wlowi/PPMInspect/PPMInspect/ScopeScreen.cpp

/*
  PPMInspect. A PPM signal analysis tool.

  MIT License

  Copyright (c) 2023 wlowi

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
  THE SOFTWARE IS PROVIDED "AS IS", WITHOUT WARRANTY OF ANY KIND, EXPRESS OR
  IMPLIED, INCLUDING BUT NOT LIMITED TO THE WARRANTIES OF MERCHANTABILITY,
  FITNESS FOR A PARTICULAR PURPOSE AND NONINFRINGEMENT. IN NO EVENT SHALL THE
  AUTHORS OR COPYRIGHT HOLDERS BE LIABLE FOR ANY CLAIM, DAMAGES OR OTHER
  LIABILITY, WHETHER IN AN ACTION OF CONTRACT, TORT OR OTHERWISE, ARISING FROM,
  OUT OF OR IN CONNECTION WITH THE SOFTWARE OR THE USE OR OTHER DEALINGS IN THE
  SOFTWARE.
*/

#include "ScopeScreen.h"

/* Config */
extern config_t settings;

/*
 * |012345678901234567891|
 * |100uO2V T+2.0V D1000u|
 */

#define ROW_COUNT 1

#define TRIGGER_MODES 3

const char* triggerModes[TRIGGER_MODES] = {
    "f", "+", "-"
};

#define RESOLUTION_STEPS 7

/* Resolution per grid division */
const char* resolutionSteps[RESOLUTION_STEPS] = {
    "100u","200u","500u",
    "  1m","  2m","  5m",
    " 10m"
};

#define OVERSAMPLING_STEPS 2

const char* oversamplingSteps[OVERSAMPLING_STEPS] = {
    " ",
    "O"
};

#define RANGE_STEPS 2

const char* rangeSteps[RANGE_STEPS] = {
    "2V",
    "1V"
};

uint8_t dataArray[ARRAY_SZ];
uint8_t startIndex;
uint32_t frame;

ScopeScreen::ScopeScreen(PPM& ppm) : ppmH(ppm)
{

}

void ScopeScreen::activate(TextUI* ui)
{
    startIndex = 0;
    frame = 0;
    freeze = false;

    for (uint8_t i = 0; i < ARRAY_SZ; i++) {
        dataArray[i] = 0;
    }
}

void ScopeScreen::deactivate(TextUI* ui)
{
    // Make sure we are in scope mode.
    enablePWMMode(false);
}

void ScopeScreen::update(TextUI* ui)
{
    TextUILcd* lcd = ui->getDisplay();

    uint32_t last;
    uint32_t left;
    uint8_t idx;
    long scaled;
    long divisor;
    boolean ok;

    if (freeze) {
        return;
    }

    if (pwmMode) {

        pwm_t* pwm = ppmH.getPWM();

        if (frame == 0 || frame > pwm->frames) {

            frame = pwm->frames;
            ok = false;

        }
        else if (pwmMode == PWMMODE_SERVO) {

            /* Display high pulse in range 900 - 2100 uSec. */

            last = pwm->lastUsed;
            left = pwm->frames - frame;
            frame += left;

            while (left--) {

                if (left <= PWM_HISTORY) {
                    idx = (uint8_t)((last + PWM_HISTORY - left) % PWM_HISTORY);
                    scaled = map(pwm->pulseH_usec[idx], 900, 2100, 0, 55);
                }
                else {
                    scaled = 0; // no data for this sample
                }

                dataArray[startIndex] = (scaled > 55) ? 55 : scaled;
                startIndex = (startIndex + 1) % ARRAY_SZ;
            }

            ok = true;
        }
        else if (pwmMode == PWMMODE_PCT) {

            /* Display high pulse percentage */

            last = pwm->lastUsed;
            left = pwm->frames - frame;
            frame += left;

            while (left--) {

                if (left <= PWM_HISTORY) {
                    idx = (uint8_t)((last + PWM_HISTORY - left) % PWM_HISTORY);
                    scaled = pwm->pulseH_usec[idx] + pwm->pulseL_usec[idx];
                    scaled = map(pwm->pulseH_usec[idx], 0, scaled, 0, 55);
                }
                else {
                    scaled = 0; // no data for this sample
                }

                dataArray[startIndex] = (scaled > 55) ? 55 : scaled;
                startIndex = (startIndex + 1) % ARRAY_SZ;
            }

            ok = true;
        }
        else {
            ok = false;
        }
    }
    else {
        /* The array gotten from fetchArray() is not adjusted. It is raw data from ADC.
         * 15V input is approximately 255.
         */
        ok = ppmH.fetchArray(dataArray, ARRAY_SZ, resToUSec(resolution), oversampling, triggerMode, triggerLevel, triggerDelay * 100);

        if (ok) {
        /* We need to map 15.7V == 255 to 2V == 8 because the grid size in Y direction is 8 pixel
         * and we want 2V per Y grid division.
         *
         * 2V == 8 -> 15.7V == 62.8 -> 255/62.8 = 4.06
         */
            if (range == 0) { /* 2V / div */
                divisor = 406;
            }
            else if (range == 1) { /* 1V / div */
                divisor = 203;
            }

            for (uint8_t x = 0; x < ARRAY_SZ; x++) {
                scaled = (long)dataArray[x] * 1000 / (1000 + 4 * settings.vppmAdjust);
                scaled = scaled * 100 / divisor;
                dataArray[x] = (scaled > 55) ? 55 : scaled;
            }
        }
    }

    if (ok) {
        lcd->drawGrid(dataArray, ARRAY_SZ, startIndex, 0, 8, 127, 63, grid ? 10 : 0, marker);
        marker = !marker;
    }
}

/* Resolution per pixel */
uint16_t ScopeScreen::resToUSec(uint8_t res)
{
    switch (res) {
    case 0: return 10;
    case 1: return 20;
    case 2: return 50;
    case 3: return 100;
    case 4: return 200;
    case 5: return 500;
    case 6: return 1000;
    }

    return 100;
}

/* TextUI */

const char* ScopeScreen::getHeader()
{
    return nullptr;
}

const char* ScopeScreen::getMenuName()
{
    return TextUI::copyToBuffer((const char*)F("MicroScope"));
}

uint8_t ScopeScreen::getRowCount()
{
    return pwmMode ? 1 : ROW_COUNT;
}

const char* ScopeScreen::getRowName(uint8_t row)
{
    switch (pwmMode) {
    case PWMMODE_PCT:
        return "PWM %";
    case PWMMODE_SERVO:
        return "PWM Servo";
    }

    return "";
}

void ScopeScreen::handleEvent(TextUI* ui, Event* e)
{
    if (!ui->inEditMode()) {

        if (e->getType() == EVENT_TYPE_KEY) {

            switch (e->getKey()) {

            case KEY_RESET: // long Up
                if (pwmMode == PWMMODE_SERVO)
                    pwmMode = PWMMODE_PCT;
                else if (pwmMode == PWMMODE_PCT)
                    pwmMode = PWMMODE_SERVO;
                refresh = true;
                e->markProcessed();
                break;

            case KEY_CLEAR: // long Enter
            case KEY_UP:
                ui->popScreen();
                e->markProcessed();
                break;

            case KEY_FUNCTION: // long Down
                grid = !grid;
                e->markProcessed();
                break;

            case KEY_DOWN:
                freeze = !freeze;
                e->markProcessed();
                break;
            }
        }
        else if (e->getType() == EVENT_TYPE_TICK) {
            update(ui);
        }
    }
}

bool ScopeScreen::needsRefresh()
{

    if (refresh) {
        refresh = false;
        return true;
    }

    return false;
}

uint8_t ScopeScreen::getColCount(uint8_t row)
{
    return pwmMode ? 0 : 9;
}

void ScopeScreen::getValue(uint8_t row, uint8_t col, Cell* cell)
{
    if (col == 0) {
        cell->setList(0, resolutionSteps, RESOLUTION_STEPS, resolution);
    }
    else if (col == 1) {
        cell->setList(4, oversamplingSteps, OVERSAMPLING_STEPS, oversampling);
    }
    else if (col == 2) {
        cell->setList(5, rangeSteps, RANGE_STEPS, range);
    }
    else if (col == 3) {
        cell->setLabel(8, F("T"), 1);
    }
    else if (col == 4) {
        cell->setList(9, triggerModes, TRIGGER_MODES, triggerMode);
    }
    else if (col == 5) {
        cell->setFloat1(10, triggerLevel, 3, 1, 99);
    }
    else if (col == 6) {
        cell->setLabel(13, F("V D"), 3);
    }
    else if (col == 7) {
        cell->setInt16(16, triggerDelay, 2, 0, 99);
    }
    else if (col == 8) {
        cell->setLabel(18, F("00u"), 3);
    }
}

void ScopeScreen::setValue(uint8_t row, uint8_t col, Cell* cell)
{
    if (col == 0) {
        resolution = cell->getList();
    }
    else if (col == 1) {
        oversampling = cell->getList();
    }
    else if (col == 2) {
        range = cell->getList();
    }
    else if (col == 4) {
        triggerMode = cell->getList();
    }
    else if (col == 5) {
        triggerLevel = cell->getFloat1();
    }
    else if (col == 7) {
        triggerDelay = cell->getInt16();
    }
}
