wlowi/PPMInspect/PPMInspect/Cell.cpp

/*
  PPMInspect. A PPM signal analysis tool.

  MIT License

  Copyright (c) 2023 wlowi

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
  THE SOFTWARE IS PROVIDED "AS IS", WITHOUT WARRANTY OF ANY KIND, EXPRESS OR
  IMPLIED, INCLUDING BUT NOT LIMITED TO THE WARRANTIES OF MERCHANTABILITY,
  FITNESS FOR A PARTICULAR PURPOSE AND NONINFRINGEMENT. IN NO EVENT SHALL THE
  AUTHORS OR COPYRIGHT HOLDERS BE LIABLE FOR ANY CLAIM, DAMAGES OR OTHER
  LIABILITY, WHETHER IN AN ACTION OF CONTRACT, TORT OR OTHERWISE, ARISING FROM,
  OUT OF OR IN CONNECTION WITH THE SOFTWARE OR THE USE OR OTHER DEALINGS IN THE
  SOFTWARE.
*/

#include "TextUI.h"

void Cell::render( TextUILcd *lcd, bool edit) {

    lcd->setColumn( screenCol);

    if( edit) {
        lcd->editColors();
    } else {
        lcd->normalColors();
    }

    switch( type) {
        case BOOLEAN_T:
            if( value.boolV) {
                lcd->printStr( TEXTUI_TEXT_ON, TEXTUI_TEXT_ON_OFF_length);
            } else {
                lcd->printStr( TEXTUI_TEXT_OFF, TEXTUI_TEXT_ON_OFF_length);
            }
            break;

        case INT8_T:
            lcd->printInt( value.intV, (value.size == 0) ? 4 : value.size);
            break;

        case INT16_T:
            lcd->printInt( value.intV, (value.size == 0) ? 6 : value.size);
            break;

        case INT32_T:
            lcd->printLong( value.intV, (value.size == 0) ? 10 : value.size);
            break;

        case FLOAT1:
            lcd->printFixFloat1( value.intV, value.size);
            break;

        case FLOAT2:
            lcd->printFixFloat2( value.intV, value.size);
            break;

        case STRING_T:
            if( edit) {
                lcd->printStr( value.string, value.size, (int8_t)value.intV);
            } else {
                lcd->printStr( value.string, value.size);
            }
            break;

        case LABEL_T:
            lcd->printStr( value.label, value.size);
            break;

        case FLABEL_T:
            lcd->printStr( value.flabel, value.size);
            break;

        case LIST_T:
            lcd->printStr( value.list[value.intV], value.size);
            break;

        case BLANK_T:
        default:
            // ignore
            break;
    }
}

bool Cell::edit( Event *event) {

    bool changed = false;

    if( !event->pending() || (event->getType() != EVENT_TYPE_KEY)) {
        return changed;
    }

    switch( type) {
    case BOOLEAN_T:
        if( (event->getKey() == KEY_DOWN) || (event->getKey() == KEY_UP) ) {
            value.boolV = ! value.boolV;
            event->markProcessed();
            changed = true;
        }
        break;

    case INT8_T:
    case INT16_T:
    case INT32_T:
    case FLOAT1:
    case FLOAT2:
        if( event->getKey() == KEY_DOWN) {
            value.intV -= event->getCount();
            event->markProcessed();
            changed = true;
        } else if( event->getKey() == KEY_UP) {
            value.intV += event->getCount();
            event->markProcessed();
            changed = true;
        } else if( event->getKey() == KEY_CLEAR) {
            value.intV = 0;
            event->markProcessed();
            changed = true;
        }

        if( value.intV > numericMax) {
            value.intV = numericMax;
        }
        if( value.intV < numericMin) {
            value.intV = numericMin;
        }

        break;

    case STRING_T:
        if( event->getKey() == KEY_ENTER) {
            if( value.intV >= (value.size-1)) {
                /* intV = character index for editing.
                 * Done when we move beyond sting length.
                 */
                break;
            } else {
                /* Move to next character in string */
                value.intV++;
                event->markProcessed();
            }
            changed = true;
        } else if( event->getKey() == KEY_DOWN) {
            /* Previous letter in alphabet. */
            value.string[value.intV] -= event->getCount();
            event->markProcessed();
            changed = true;
        } else if( event->getKey() == KEY_UP) {
            /* Next letter in alphabet. */
            value.string[value.intV] += event->getCount();
            event->markProcessed();
            changed = true;
        } else if( event->getKey() == KEY_CLEAR) {
            /* Space character. */
            value.string[value.intV] = ' ';
            event->markProcessed();
            changed = true;
        }

        if( value.string[value.intV] < ' ') {
            value.string[value.intV] = ' ';
        }
        if( value.string[value.intV] > (char)126) {
            value.string[value.intV] = (char)126;
        }

        break;

    case LIST_T:
        if( event->getKey() == KEY_DOWN) {
            value.intV -= event->getCount();
            if( value.intV < 0) {
                value.intV = 0;
            }
            event->markProcessed();
            changed = true;
        } else if( event->getKey() == KEY_UP) {
            value.intV += event->getCount();
            if( value.intV >= value.count) {
                value.intV = value.count-1;
            }
            event->markProcessed();
            changed = true;
        }
        break;
    
    case BLANK_T:
    default:
        // ignore
        break;
    }

    return changed;
}

bool Cell::isEditable() {

    return ((type != LABEL_T) && (type != FLABEL_T) && (type != BLANK_T));
}

void Cell::setBlank() {

    type = BLANK_T;
}

void Cell::setBool( uint8_t screenX, bool v) {

    screenCol = screenX;
    type = BOOLEAN_T;
    value.boolV = v;
}

void Cell::setInt8( uint8_t screenX, int8_t v, uint8_t width, int16_t nmin, int16_t nmax) {

    screenCol = screenX;
    type = INT8_T;
    value.intV = v;
    value.size = width; /* display width */
    numericMin = nmin;
    numericMax = nmax;
}

void Cell::setInt16( uint8_t screenX, int16_t v, uint8_t width, int16_t nmin, int16_t nmax) {

    screenCol = screenX;
    type = INT16_T;
    value.intV = v;
    value.size = width; /* display width */
    numericMin = nmin;
    numericMax = nmax;
}

void Cell::setInt32( uint8_t screenX, int32_t v, uint8_t width, int32_t nmin, int32_t nmax) {

    screenCol = screenX;
    type = INT32_T;
    value.intV = v;
    value.size = width; /* display width */
    numericMin = nmin;
    numericMax = nmax;
}

void Cell::setFloat1( uint8_t screenX, fixfloat1_t v, uint8_t width, fixfloat1_t nmin, fixfloat1_t nmax) {

    screenCol = screenX;
    type = FLOAT1;
    value.intV = v;
    value.size = width; /* display width */
    numericMin = nmin;
    numericMax = nmax;
}

void Cell::setFloat2( uint8_t screenX, fixfloat2_t v, uint8_t width, fixfloat2_t nmin, fixfloat2_t nmax) {

    screenCol = screenX;
    type = FLOAT2;
    value.intV = v;
    value.size = width; /* display width */
    numericMin = nmin;
    numericMax = nmax;
}

void Cell::setString( uint8_t screenX, char *v, uint8_t sz) {

    screenCol = screenX;
    type = STRING_T;
    value.string = v;
    value.size = sz;
    value.intV = 0; // character index for editing.
}

void Cell::setLabel( uint8_t screenX, const char *v, uint8_t sz) {

    screenCol = screenX;
    type = LABEL_T;
    value.label = v;
    value.size = sz;
}

#ifdef ARDUINO
void Cell::setLabel(uint8_t screenX, const __FlashStringHelper *v, uint8_t sz) {

    screenCol = screenX;
    type = FLABEL_T;
    value.flabel = v;
    value.size = sz;
}
#endif

void Cell::setList( uint8_t screenX, const char* const* v, uint8_t count, uint8_t curr) {

    uint8_t i;
    uint8_t sz;

    screenCol = screenX;
    type = LIST_T;
    value.list = v;
    value.count = count;
    value.intV = (curr >= count) ? count-1 : curr;

    /* determine max option string length */
    value.size = 0;
    for( i=0; i<count; i++) {
        sz = strlen( v[i]);
        if( sz > value.size) { value.size = sz; }
    }
}

bool Cell::getBool() const {

    return value.boolV;
} 

int8_t Cell::getInt8() const {

    return (int8_t)value.intV;
}

int16_t Cell::getInt16() const {

    return (int16_t)value.intV;
}

int32_t Cell::getInt32() const {

    return value.intV;
}

fixfloat1_t Cell::getFloat1() const {

    return (fixfloat1_t)value.intV;
}

fixfloat2_t Cell::getFloat2() const {

    return (fixfloat2_t)value.intV;
}

char *Cell::getString() const {

    return value.string;
}

uint8_t Cell::getList() const {

    return (uint8_t)value.intV;
}
