wlowi/PPMInspect/PPMInspect/TextUI.cpp

/*
  TextUI. A simple text based UI.

  MIT License

  Copyright (c) 2023 wlowi

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
  THE SOFTWARE IS PROVIDED "AS IS", WITHOUT WARRANTY OF ANY KIND, EXPRESS OR
  IMPLIED, INCLUDING BUT NOT LIMITED TO THE WARRANTIES OF MERCHANTABILITY,
  FITNESS FOR A PARTICULAR PURPOSE AND NONINFRINGEMENT. IN NO EVENT SHALL THE
  AUTHORS OR COPYRIGHT HOLDERS BE LIABLE FOR ANY CLAIM, DAMAGES OR OTHER
  LIABILITY, WHETHER IN AN ACTION OF CONTRACT, TORT OR OTHERWISE, ARISING FROM,
  OUT OF OR IN CONNECTION WITH THE SOFTWARE OR THE USE OR OTHER DEALINGS IN THE
  SOFTWARE.
*/

#include "TextUI.h"

#define DEFAULT_STRINGBUFFER_LEN 20

static char *stringBuffer = nullptr;
static uint8_t stringBufferSize = 0;

TextUI::TextUI() {

}

TextUI::TextUI( uint8_t bufferSize) {

    stringBufferSize = bufferSize;
    stringBuffer = new char[stringBufferSize]; 
}

/* static */
char* TextUI::copyToBuffer( const char* PROGMEM v) {

    uint8_t i = 0;

    if( stringBuffer == nullptr) {
        stringBufferSize = DEFAULT_STRINGBUFFER_LEN;
        stringBuffer = new char[stringBufferSize];
    }

    while (i < stringBufferSize && pgm_read_byte( v+i) != 0) {
        stringBuffer[i] = pgm_read_byte( v+i);
        i++;
    }

    if( i == stringBufferSize) i--;

    stringBuffer[i] = '\0';

    return stringBuffer;
}

void TextUI::setTimer( uiTimer_t t_msec) {

  if( t_msec == 0) { // Disable Timer
    nextTimer_msec = timer_msec = 0;
  } else {
    timer_msec = (t_msec < 10) ? 10 : t_msec;
    nextTimer_msec = millis() + timer_msec;
  }
}

void TextUI::setDisplay( TextUILcd *lcd) {

  display = lcd;
}

void TextUI::setInput( TextUIInput *in) {

  if( inputQueue == nullptr) {
    inputQueue = in;
  } else {
    inputQueue->append( in);
  }
}

void TextUI::setHomeScreen( TextUIScreen *scr) {

  stackPtr = 0;
  CURRENT_SCREEN = homeScreen = scr;
  refresh = REFRESH_FULL;
}

Event *TextUI::getEvent() {

  unsigned long now = millis();
  TextUIInput *lastInput;
  
  event.setNoEvent(); 
  
  /* First check input queues.
   * Queues are checked round robin.
   * If there are two queues and the first queue had an event pending,
   * next time the second queue is checked first. 
   */
  if( currentInput == nullptr)
  {
    currentInput = inputQueue;
  }

  if( currentInput != nullptr)
  {
    lastInput = currentInput;

    do
    {
      if( currentInput->pending() )
      {
        currentInput->setEvent( &event);
      }

      currentInput = currentInput->getNext();
      if( currentInput == nullptr)
      {
        currentInput = inputQueue;
      }

      if( event.getType() != EVENT_TYPE_NONE) { break; }

    } while( currentInput != lastInput);
  }

  if( event.getType() == EVENT_TYPE_NONE ) {

    if( timer_msec && (now >= nextTimer_msec)) {
    
      nextTimer_msec += timer_msec;
      if( nextTimer_msec <= now) {
	nextTimer_msec = now + timer_msec;
      }
      event.setTimerEvent();
    
    } else if( now >= nextTick_msec ) {

      nextTick_msec += EVENT_TICK_msec;
      if( nextTick_msec <= now) {
      	nextTick_msec = now + EVENT_TICK_msec;
      }
      event.setTickEvent();
    }
  }

  return &event;
}

void TextUI::setReversedNav( boolean v) {

  reversedNav = v;
}

boolean TextUI::isReversedNav() {

  return reversedNav;
}

boolean TextUI::inEditMode() {

  return handler.inEditMode();
}

/* Cancel edit for this table */
void TextUI::cancelEdit(TextUIScreen *toCancel) {

  handler.cancelEdit( toCancel);
}

void TextUI::handle( Event *ev) {

  if( CURRENT_SCREEN == nullptr || display == nullptr) {
    return;
  }

  if( refresh == REFRESH_FULL) {
    if( itemPopped) {
      handler.set( this, CURRENT_SCREEN, CURRENT_SCREEN->getSelection());
      itemPopped = false;
    } else {
      handler.set( this, CURRENT_SCREEN);
    }
    refresh = REFRESH_OK;
  } else if( refresh == REFRESH_SCREEN) {
    handler.forceRefresh();
    refresh = REFRESH_OK;
  }

  handler.process( this, display, ev);
}

void TextUI::toHome() {

  UILOG("toHome()\n");

  stackPtr = 0;
  CURRENT_SCREEN = homeScreen;
  refresh = REFRESH_FULL;
}

void TextUI::toScreen( TextUIScreen *scr) {

  UILOG("toScreen()\n");

  stackPtr = 0;
  CURRENT_SCREEN = scr;
  refresh = REFRESH_FULL;
}

void TextUI::switchScreen( TextUIScreen *scr) {

  UILOGV("switchScreen(): %d\n", stackPtr);

  CURRENT_SCREEN = scr;
  refresh = REFRESH_FULL;
}

void TextUI::pushScreen( TextUIScreen *scr) {
  
  if( stackPtr < TEXTUI_SCREENSTACK_SZ-1) {
    stackPtr++;
  }

  UILOGV("pushScreen(): %d\n", stackPtr);

  CURRENT_SCREEN = scr;
  refresh = REFRESH_FULL;
}

void TextUI::popScreen() {
  
  if( stackPtr > 0) {
    stackPtr--;
  }

  UILOGV("popScreen(): %d\n", stackPtr);

  refresh = REFRESH_FULL;
  itemPopped = true;
}
